Architeuthis-Flux/breadWare/IMG_1637.jpeg

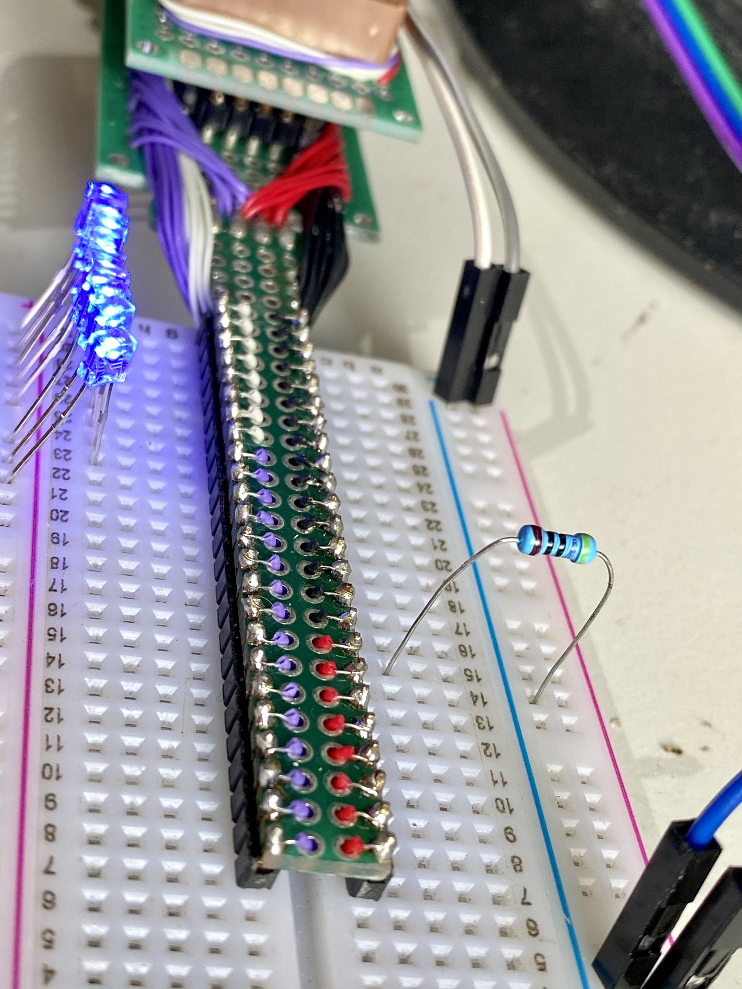
IMG_1637.jpeg
