Architeuthis-Flux/breadWare/IMG_1644.jpeg

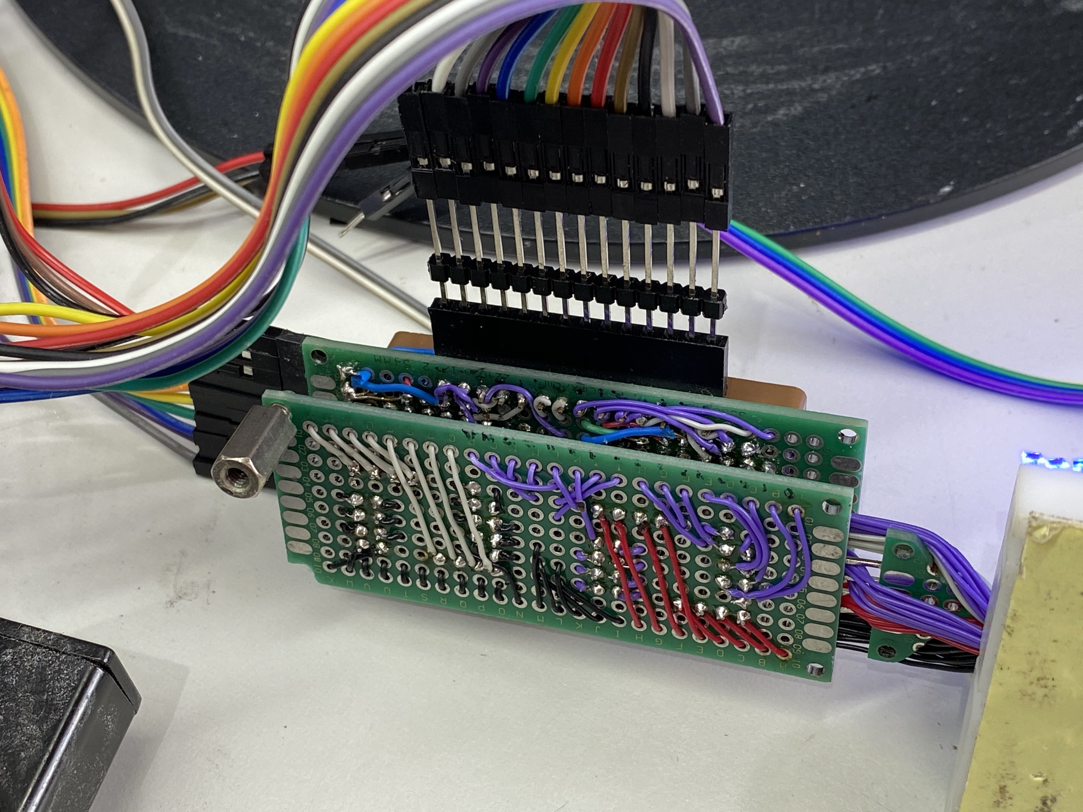
IMG_1644.jpeg
