Architeuthis-Flux/breadWare/IMG_1645.jpeg

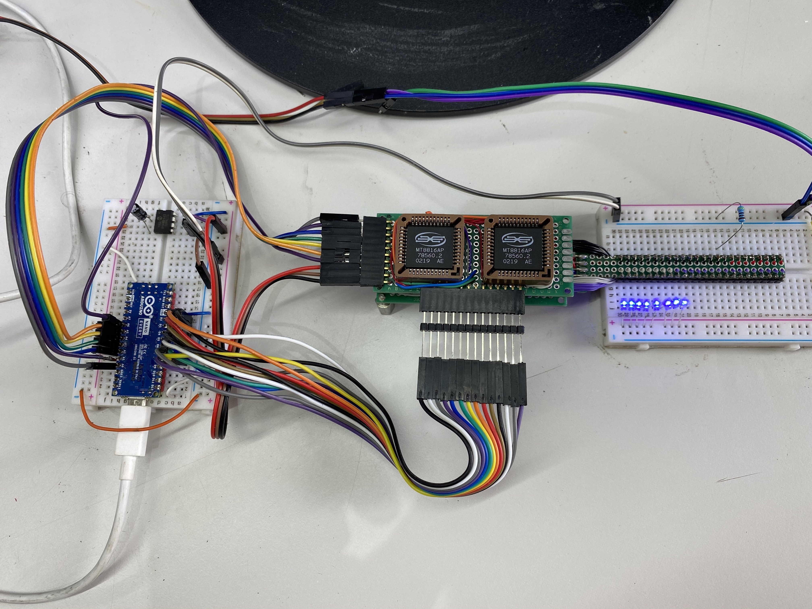
IMG_1645.jpeg
